CoolNamesAllTaken/radar-speed-sign/affinity/radar_speed_sign.png

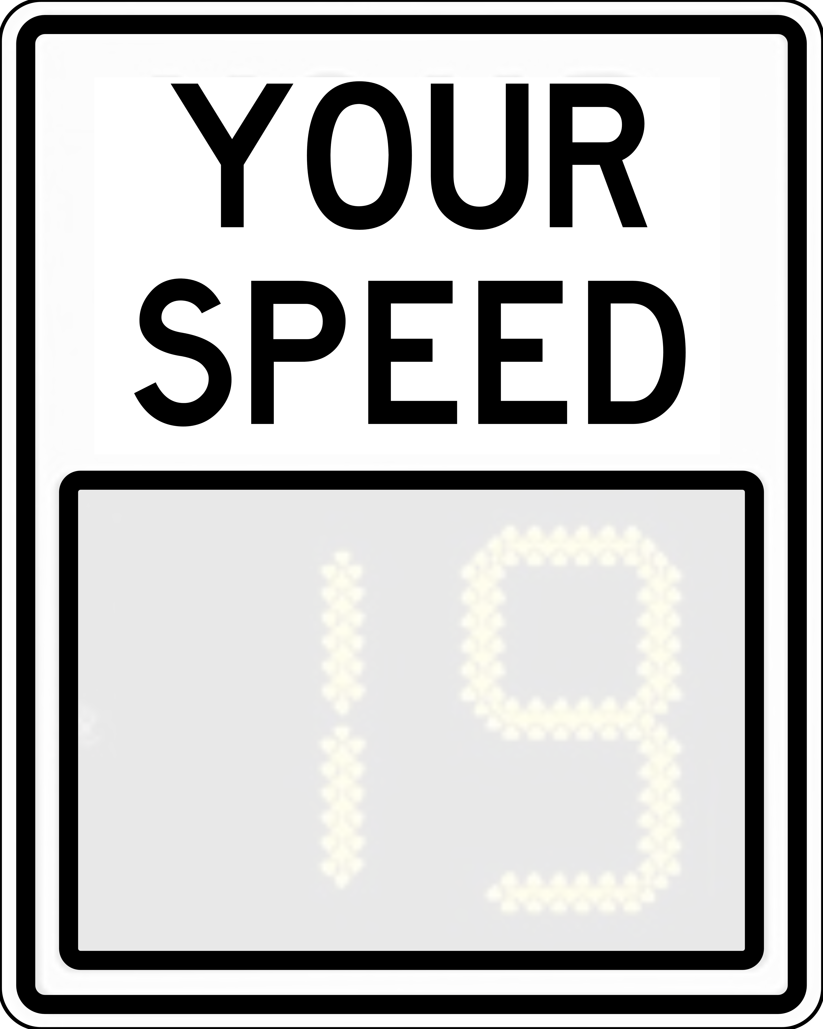
affinity/radar_speed_sign.png
