CoolNamesAllTaken/radar-speed-sign/references/andreas_spiess_radars_comparison.png

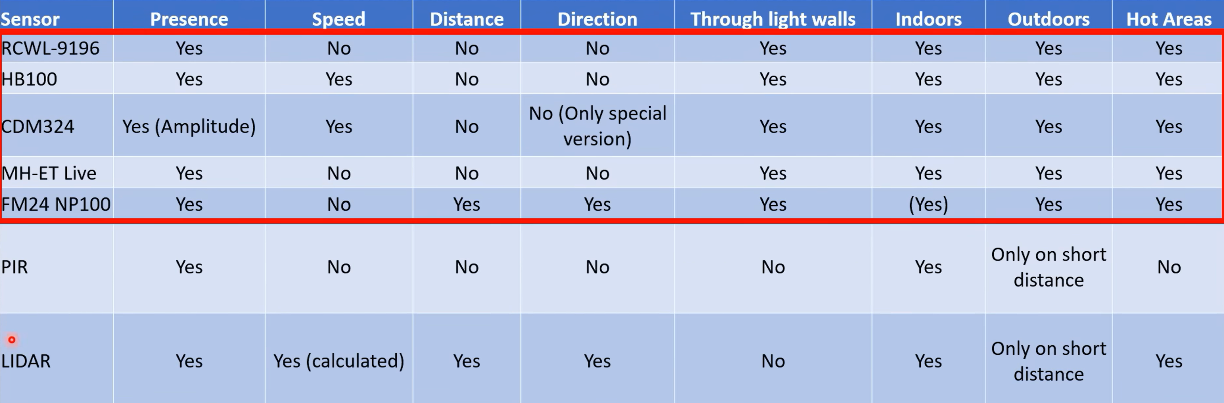
references/andreas_spiess_radars_comparison.png
