CoolNamesAllTaken/radar-speed-sign/references/CDM324 Doppler Speed Sensor, with FFTs! - Limpkin's blog_files/cdm324_digital.PNG

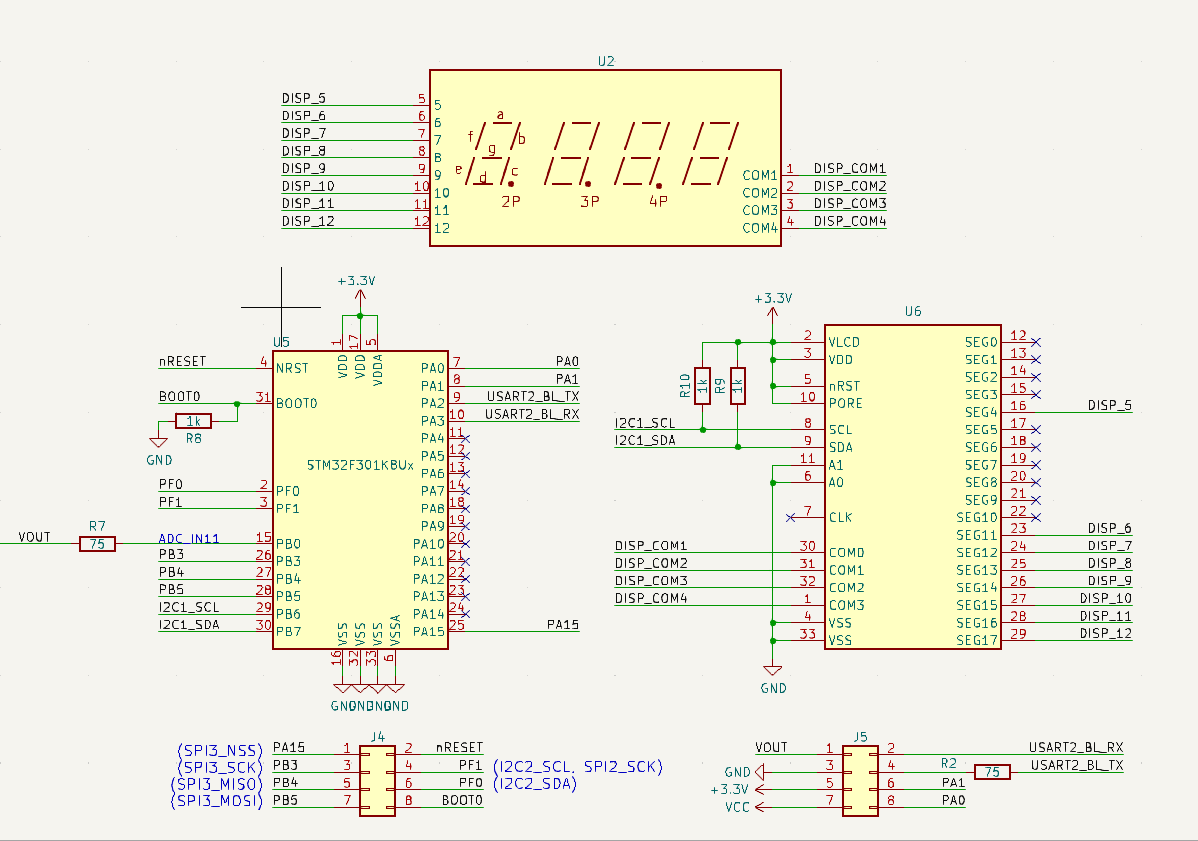
references/CDM324 Doppler Speed Sensor, with FFTs! - Limpkin's blog_files/cdm324_digital.PNG
