CoolNamesAllTaken/radar-speed-sign/references/CDM324 Doppler Speed Sensor, with FFTs! - Limpkin's blog_files/cdm_and_exp.JPG

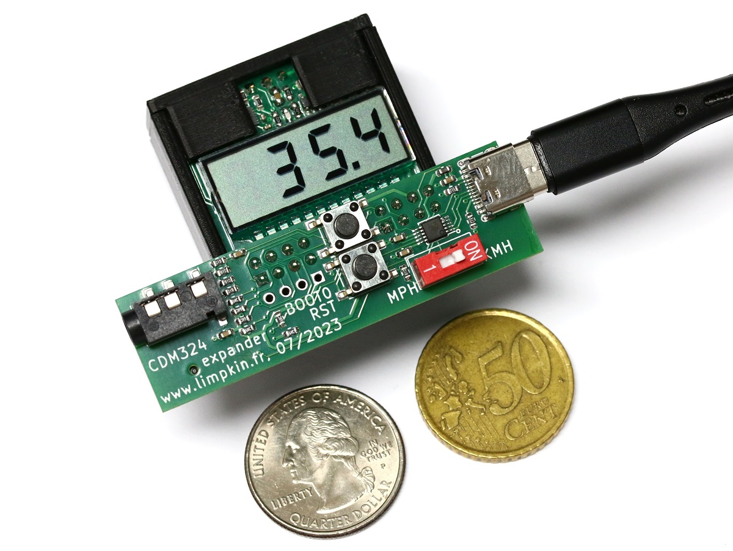
references/CDM324 Doppler Speed Sensor, with FFTs! - Limpkin's blog_files/cdm_and_exp.JPG
