CoolNamesAllTaken/radar-speed-sign/references/CDM324 Doppler Speed Sensor, with FFTs! - Limpkin's blog_files/cdm_pcb.JPG

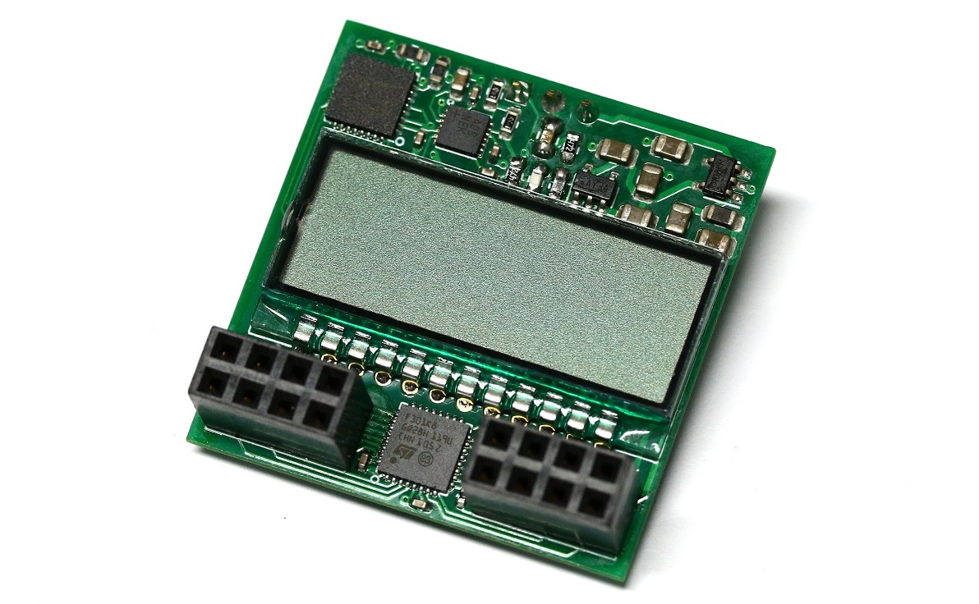
references/CDM324 Doppler Speed Sensor, with FFTs! - Limpkin's blog_files/cdm_pcb.JPG
