CoolNamesAllTaken/radar-speed-sign/references/CDM324 Doppler Speed Sensor, with FFTs! - Limpkin's blog_files/cdm_s21.PNG

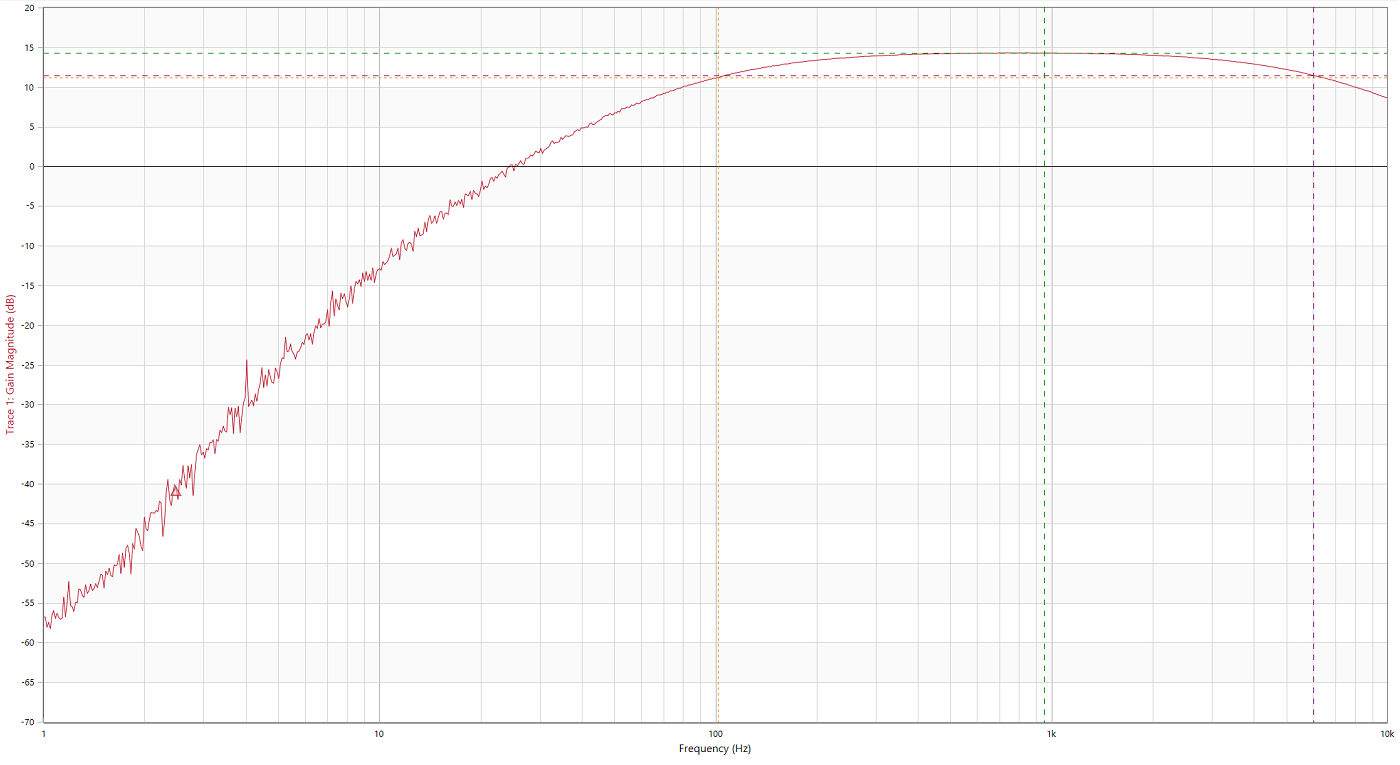
references/CDM324 Doppler Speed Sensor, with FFTs! - Limpkin's blog_files/cdm_s21.PNG
