CoolNamesAllTaken/radar-speed-sign/references/CDM324 Doppler Speed Sensor, with FFTs! - Limpkin's blog_files/disappearing_noise.jpg

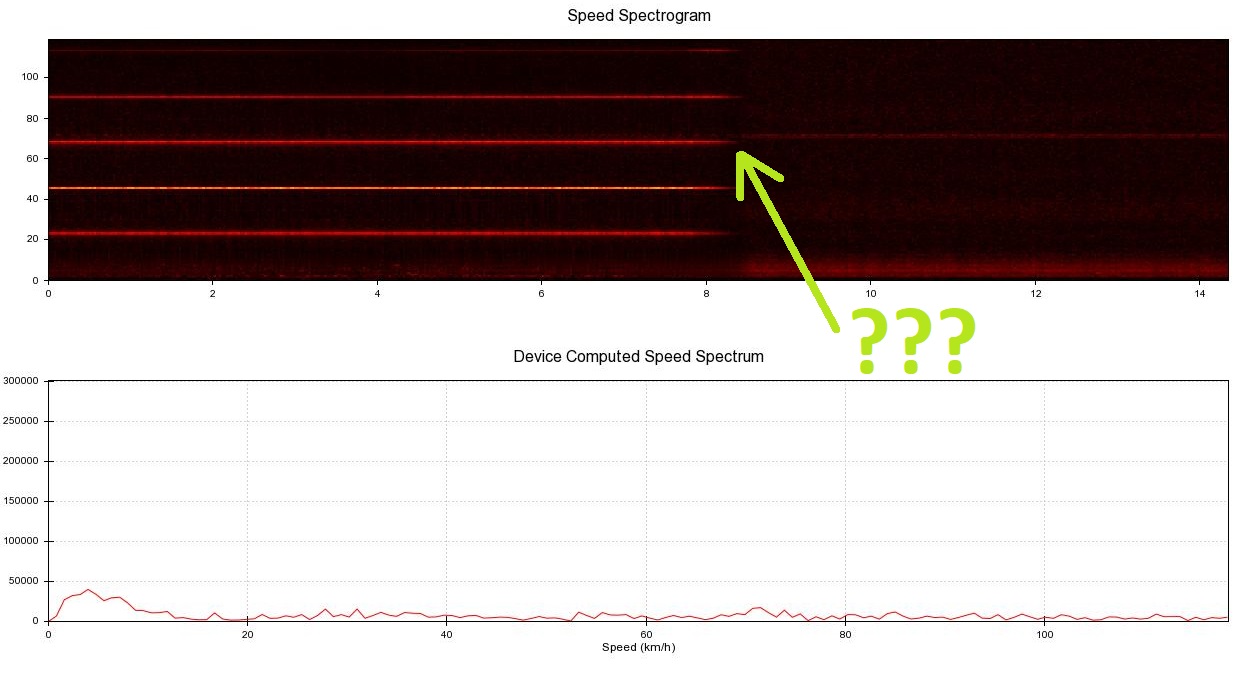
references/CDM324 Doppler Speed Sensor, with FFTs! - Limpkin's blog_files/disappearing_noise.jpg
