CoolNamesAllTaken/radar-speed-sign/references/CDM324 Doppler Speed Sensor, with FFTs! - Limpkin's blog_files/inv_opamp_noise_calc.png

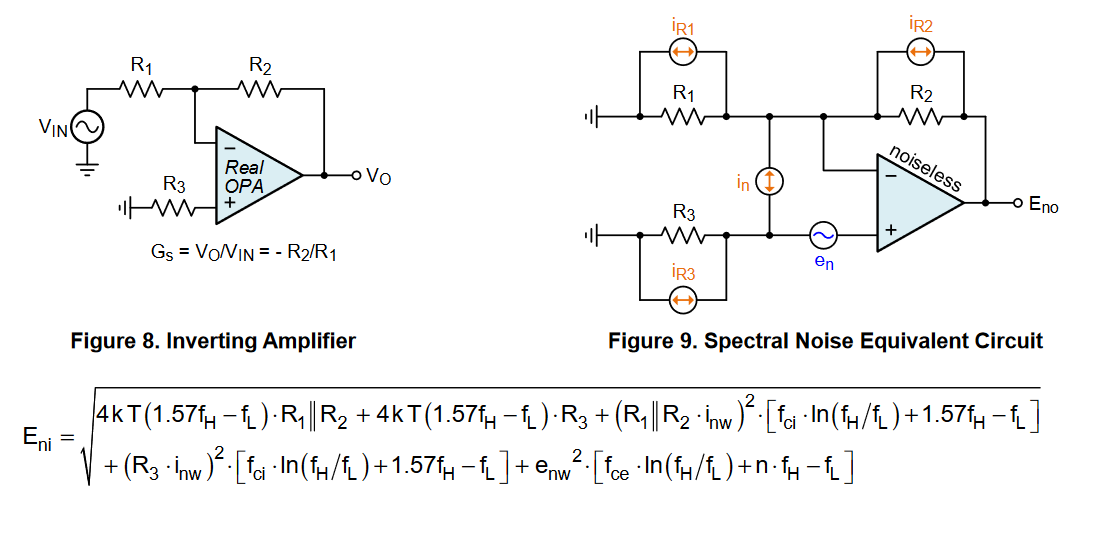
references/CDM324 Doppler Speed Sensor, with FFTs! - Limpkin's blog_files/inv_opamp_noise_calc.png
