CoolNamesAllTaken/radar-speed-sign/references/CDM324 Doppler Speed Sensor, with FFTs! - Limpkin's blog_files/max9814_gain.PNG

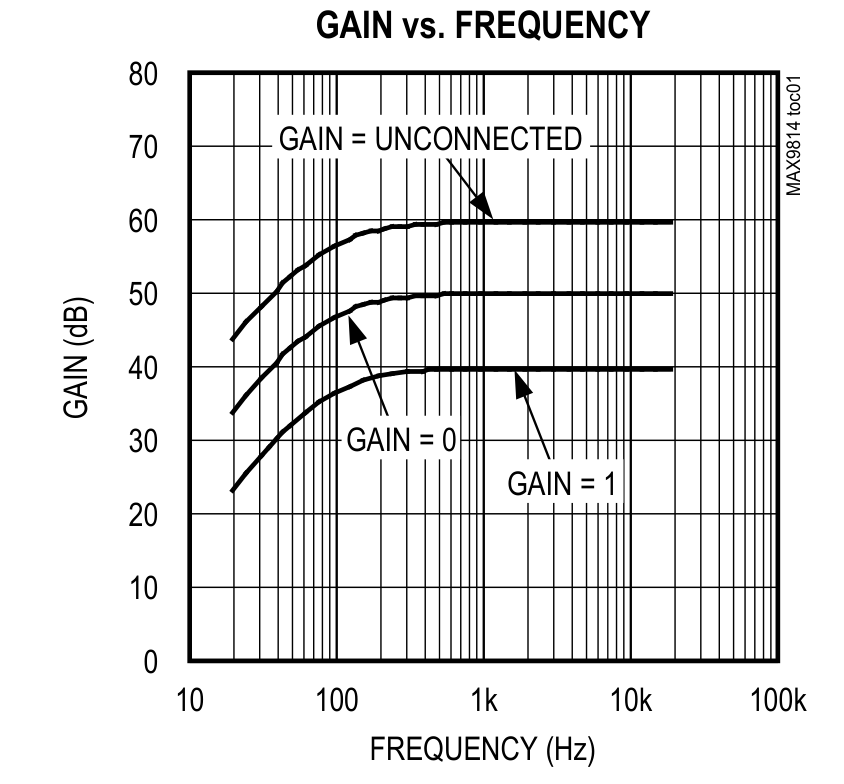
references/CDM324 Doppler Speed Sensor, with FFTs! - Limpkin's blog_files/max9814_gain.PNG
