CoolNamesAllTaken/radar-speed-sign/references/CDM324 Doppler Speed Sensor, with FFTs! - Limpkin's blog_files/Omicron_BODE-100.jpg

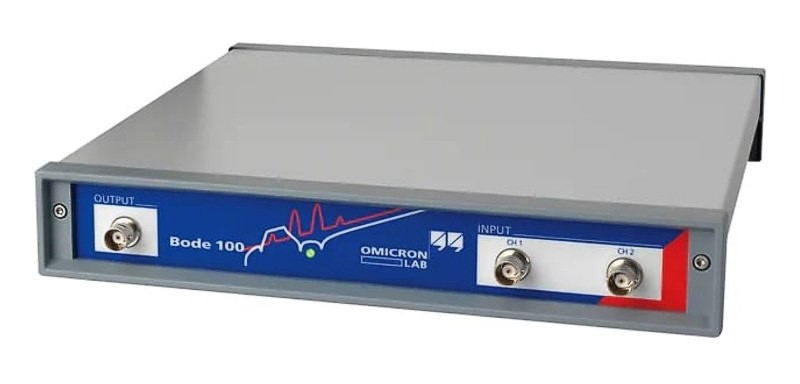
references/CDM324 Doppler Speed Sensor, with FFTs! - Limpkin's blog_files/Omicron_BODE-100.jpg
