CoolNamesAllTaken/radar-speed-sign/references/CDM324 Doppler Speed Sensor, with FFTs! - Limpkin's blog_files/tn_display.PNG

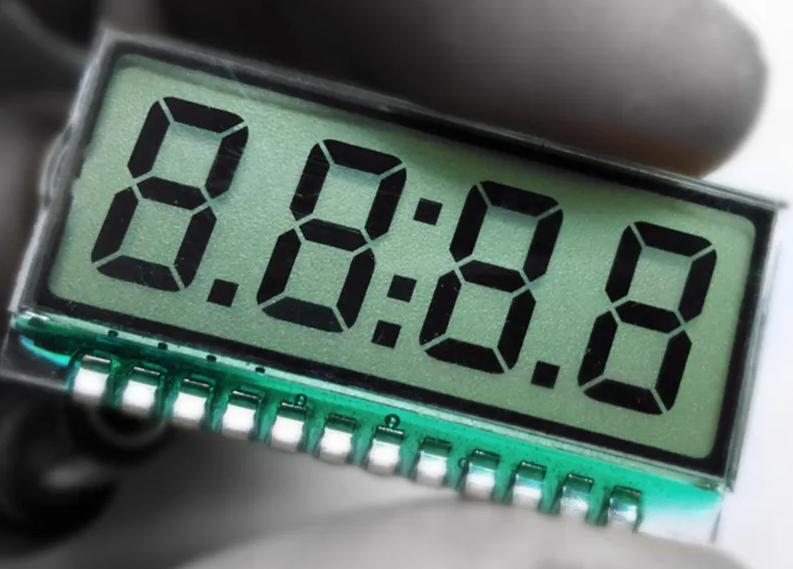
references/CDM324 Doppler Speed Sensor, with FFTs! - Limpkin's blog_files/tn_display.PNG
