CoolNamesAllTaken/radar-speed-sign/references/CDM324 Doppler Speed Sensor, with FFTs! - Limpkin's blog_files/transf_func_cdm324_updated_filter.png

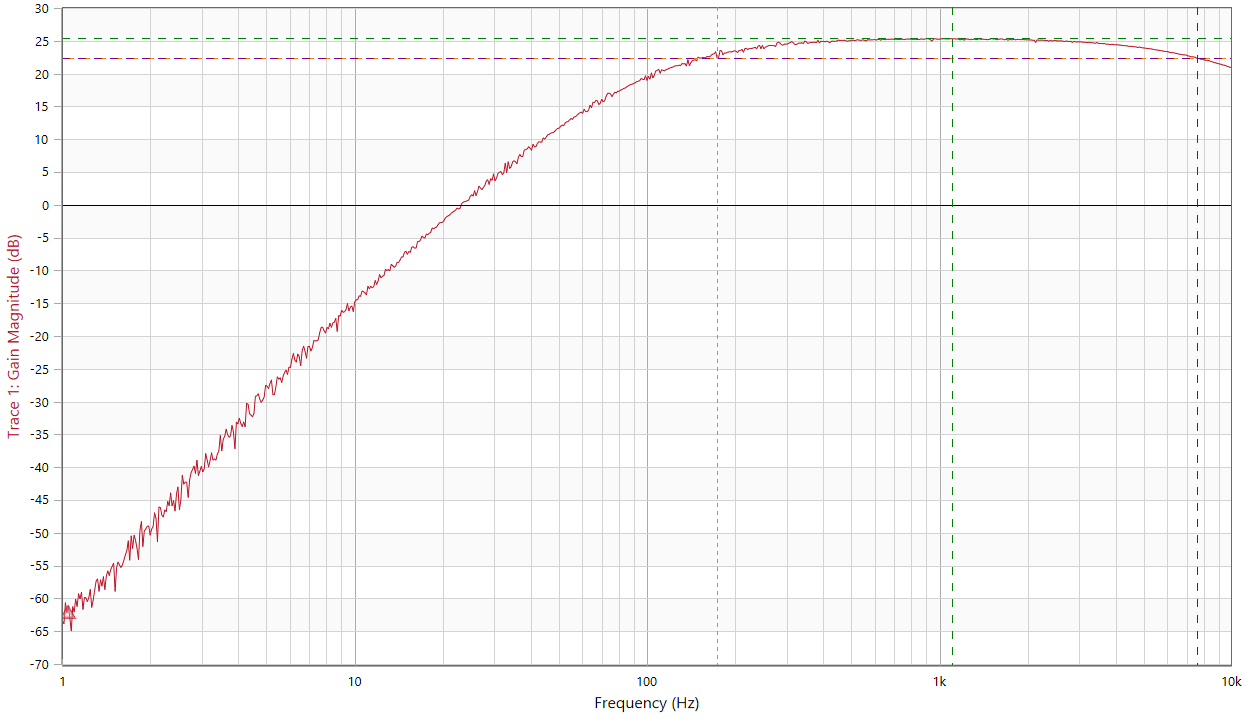
references/CDM324 Doppler Speed Sensor, with FFTs! - Limpkin's blog_files/transf_func_cdm324_updated_filter.png
