CoolNamesAllTaken/radar-speed-sign/references/CDM324 Doppler Speed Sensor, with FFTs! - Limpkin's blog_files/updated_first_stage.PNG

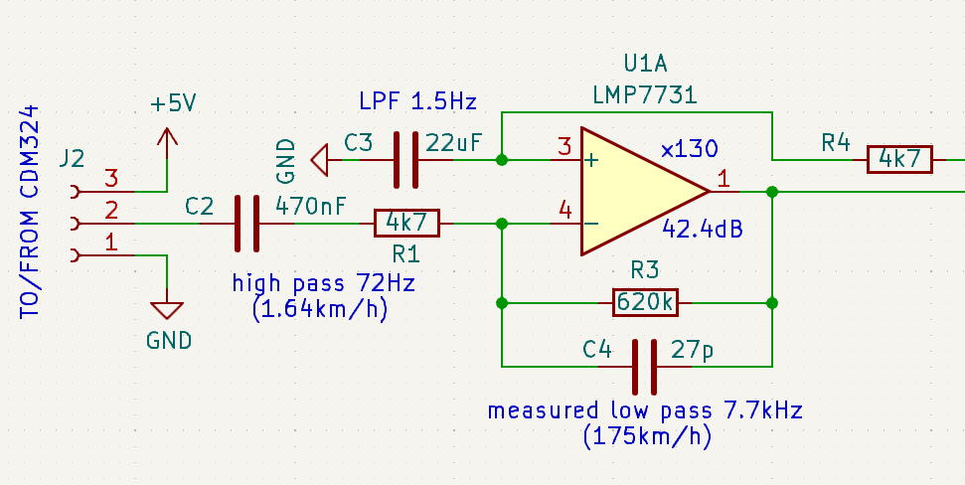
references/CDM324 Doppler Speed Sensor, with FFTs! - Limpkin's blog_files/updated_first_stage.PNG
