CoolNamesAllTaken/radar-speed-sign/references/CDM324 Doppler Speed Sensor, with FFTs! - Limpkin's blog_files/usb_isolator.png

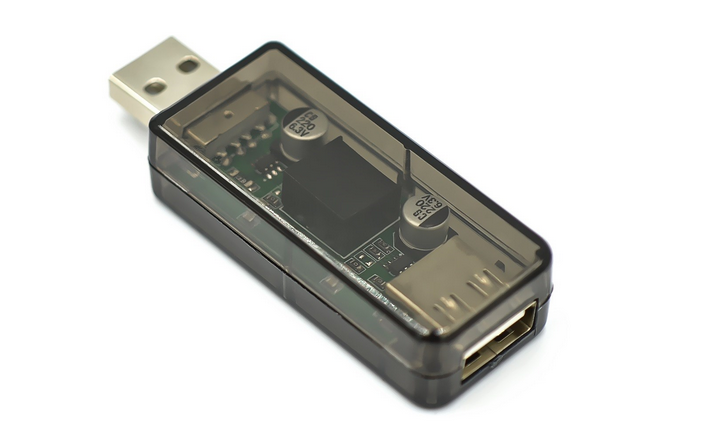
references/CDM324 Doppler Speed Sensor, with FFTs! - Limpkin's blog_files/usb_isolator.png
