CoolNamesAllTaken/radar-speed-sign/references/Radar Module EIRP Radiation Patterns for RCWL-0516, HB100, CDM324_files/CDM324-Radar-Module-Antenna-Pattern-Anechoic-Chamber-Photo-1-683x1024.jpg

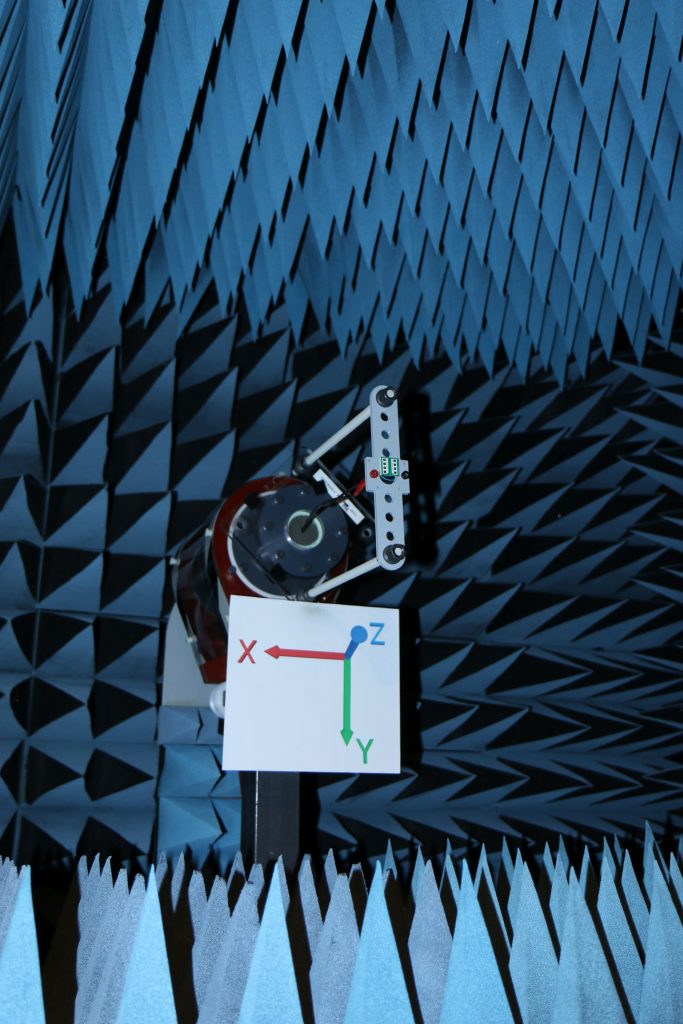
references/Radar Module EIRP Radiation Patterns for RCWL-0516, HB100, CDM324_files/CDM324-Radar-Module-Antenna-Pattern-Anechoic-Chamber-Photo-1-683x1024.jpg
