CoolNamesAllTaken/radar-speed-sign/references/Radar Module EIRP Radiation Patterns for RCWL-0516, HB100, CDM324_files/HB100-Module-PCB.jpg

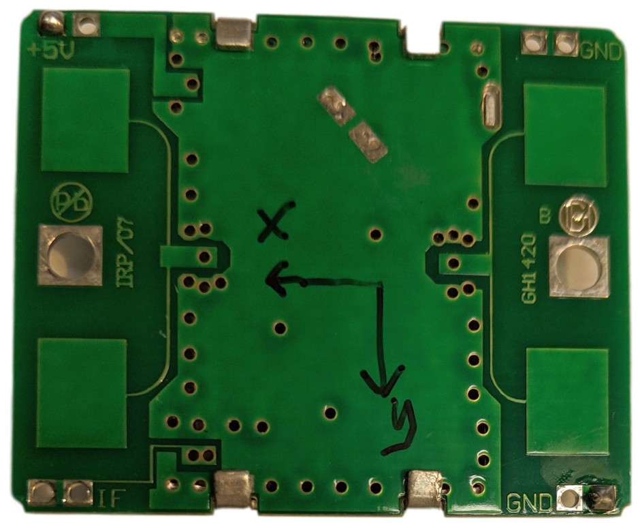
references/Radar Module EIRP Radiation Patterns for RCWL-0516, HB100, CDM324_files/HB100-Module-PCB.jpg
