CoolNamesAllTaken/radar-speed-sign/references/Radar Module EIRP Radiation Patterns for RCWL-0516, HB100, CDM324_files/HB100-Radar-Module-Antenna-Pattern-Anechoic-Chamber-Photo-1-1024x647.jpg

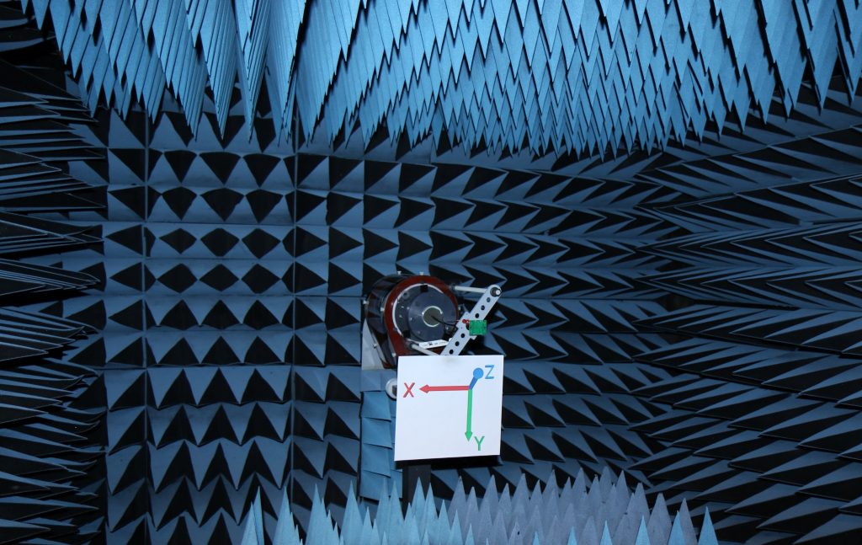
references/Radar Module EIRP Radiation Patterns for RCWL-0516, HB100, CDM324_files/HB100-Radar-Module-Antenna-Pattern-Anechoic-Chamber-Photo-1-1024x647.jpg
