CoolNamesAllTaken/radar-speed-sign/references/Radar Module EIRP Radiation Patterns for RCWL-0516, HB100, CDM324_files/HB100-Radar-Module-Antenna-Pattern-Anechoic-Chamber-Photo-4-1024x683.jpg

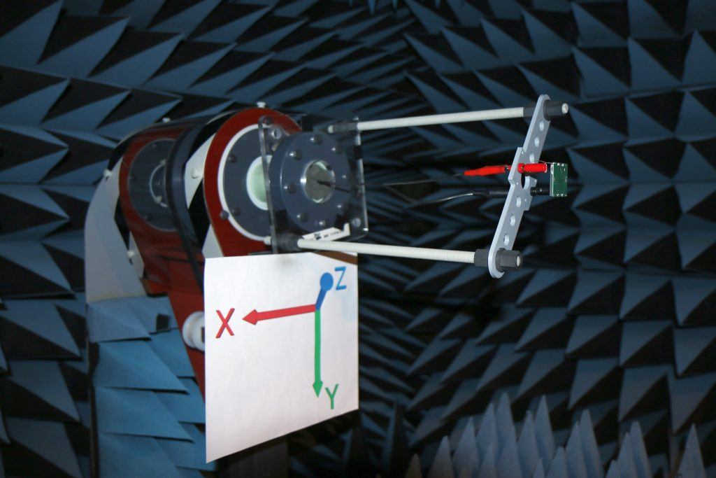
references/Radar Module EIRP Radiation Patterns for RCWL-0516, HB100, CDM324_files/HB100-Radar-Module-Antenna-Pattern-Anechoic-Chamber-Photo-4-1024x683.jpg
