CoolNamesAllTaken/radar-speed-sign/references/Radar Module EIRP Radiation Patterns for RCWL-0516, HB100, CDM324_files/RCWL-0516-Radar-Module-Antenna-Pattern-Anechoic-Chamber-Photo-1-813x1024.jpg

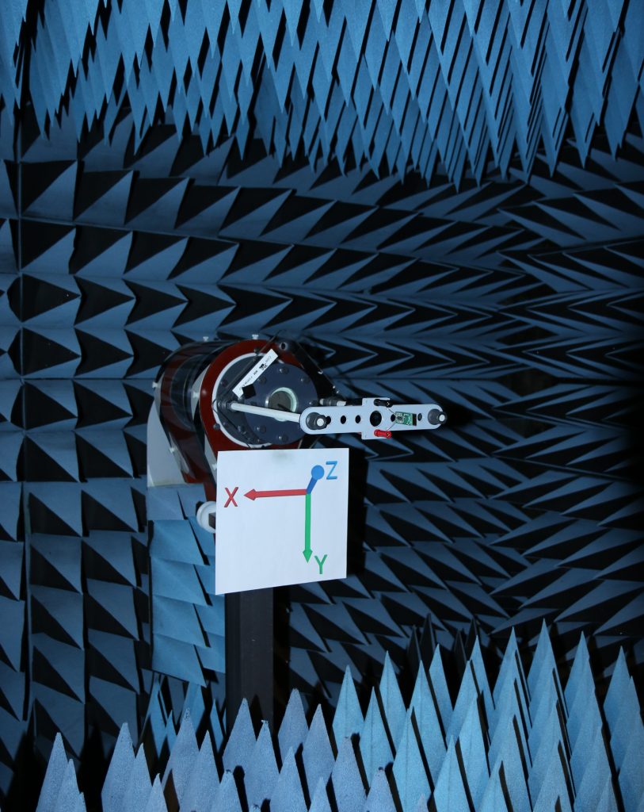
references/Radar Module EIRP Radiation Patterns for RCWL-0516, HB100, CDM324_files/RCWL-0516-Radar-Module-Antenna-Pattern-Anechoic-Chamber-Photo-1-813x1024.jpg
