CoolNamesAllTaken/radar-speed-sign/references/CDM324 Doppler Speed Sensor, with FFTs! - Limpkin's blog_files/cdm324_cur_transient_issue.png

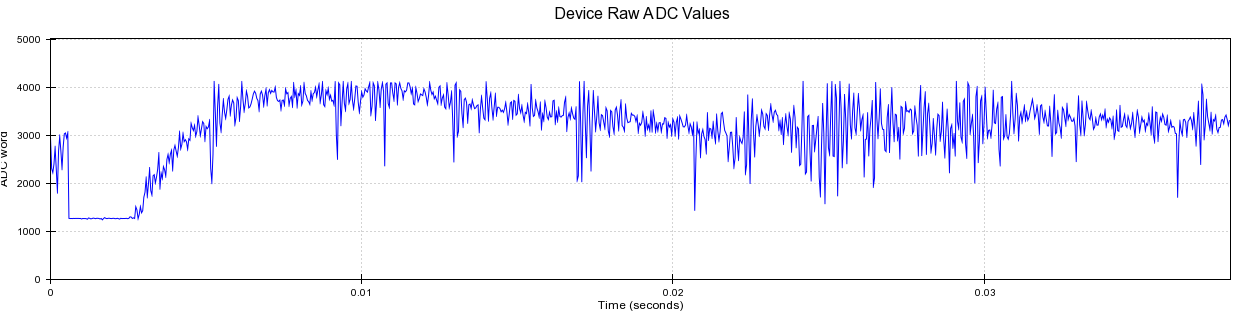
references/CDM324 Doppler Speed Sensor, with FFTs! - Limpkin's blog_files/cdm324_cur_transient_issue.png
