CoolNamesAllTaken/radar-speed-sign/ltspice/lm358_amplifier_bode.asc

C1: cap; 4.7µ
C3: cap; 4.7µ
C4: cap; 4.7µ
R1: res; 10k
R2: res; 10k
U1: UniversalOpAmp2
V1: voltage; ""; AC 1
Named nets: 3v3, 0, in, out
.ac dec 1000 1 100k
