CoolNamesAllTaken/radar-speed-sign/code/pico_cpp_radar_speed_sign/src/fft_utils.cpp

#include "fft_utils.hh"
#include "stdio.h" // for printing

const uint16_t kNumHanningSteps = 1000;
uint16_t kHanningTableUint16[kNumHanningSteps] = {
        0, 0, 1, 3, 5, 8, 12, 16, 21, 26, 32,
        39, 47, 55, 63, 73, 83, 93, 105, 117, 129,
        142, 156, 171, 186, 202, 218, 235, 253, 271, 290,
        310, 330, 351, 372, 395, 417, 441, 465, 489, 515,
        541, 567, 594, 622, 651, 680, 709, 739, 770, 802,
        834, 867, 900, 934, 969, 1004, 1040, 1076, 1113, 1151,
        1189, 1228, 1267, 1307, 1348, 1389, 1430, 1473, 1516, 1559,
        1603, 1648, 1693, 1739, 1786, 1833, 1880, 1929, 1977, 2027,
        2076, 2127, 2178, 2229, 2282, 2334, 2388, 2441, 2496, 2551,
        2606, 2662, 2718, 2776, 2833, 2891, 2950, 3009, 3069, 3129,
        3190, 3251, 3313, 3375, 3438, 3501, 3565, 3630, 3695, 3760,
        3826, 3892, 3959, 4026, 4094, 4163, 4231, 4301, 4370, 4441,
        4511, 4582, 4654, 4726, 4799, 4872, 4945, 5019, 5094, 5168,
        5244, 5319, 5395, 5472, 5549, 5626, 5704, 5783, 5861, 5940,
        6020, 6100, 6180, 6261, 6342, 6424, 6506, 6588, 6671, 6754,
        6837, 6921, 7005, 7090, 7175, 7260, 7346, 7432, 7518, 7605,
        7692, 7780, 7867, 7955, 8044, 8133, 8222, 8311, 8401, 8491,
        8581, 8672, 8763, 8854, 8946, 9038, 9130, 9222, 9315, 9408,
        9501, 9595, 9689, 9783, 9877, 9972, 10067, 10162, 10257, 10353,
        10448, 10545, 10641, 10737, 10834, 10931, 11028, 11126, 11223, 11321,
        11419, 11517, 11616, 11714, 11813, 11912, 12011, 12110, 12210, 12309,
        12409, 12509, 12609, 12710, 12810, 12910, 13011, 13112, 13213, 13314,
        13415, 13516, 13618, 13719, 13821, 13923, 14025, 14126, 14228, 14331,
        14433, 14535, 14637, 14740, 14842, 14945, 15047, 15150, 15253, 15355,
        15458, 15561, 15664, 15766, 15869, 15972, 16075, 16178, 16281, 16384,
        16487, 16590, 16693, 16796, 16899, 17002, 17104, 17207, 17310, 17413,
        17515, 17618, 17721, 17823, 17926, 18028, 18131, 18233, 18335, 18437,
        18540, 18642, 18743, 18845, 18947, 19049, 19150, 19252, 19353, 19454,
        19555, 19656, 19757, 19858, 19958, 20058, 20159, 20259, 20359, 20459,
        20558, 20658, 20757, 20856, 20955, 21054, 21152, 21251, 21349, 21447,
        21545, 21642, 21740, 21837, 21934, 22031, 22127, 22223, 22320, 22415,
        22511, 22606, 22701, 22796, 22891, 22985, 23079, 23173, 23267, 23360,
        23453, 23546, 23638, 23730, 23822, 23914, 24005, 24096, 24187, 24277,
        24367, 24457, 24546, 24635, 24724, 24813, 24901, 24988, 25076, 25163,
        25250, 25336, 25422, 25508, 25593, 25678, 25763, 25847, 25931, 26014,
        26097, 26180, 26262, 26344, 26426, 26507, 26588, 26668, 26748, 26828,
        26907, 26985, 27064, 27142, 27219, 27296, 27373, 27449, 27524, 27600,
        27674, 27749, 27823, 27896, 27969, 28042, 28114, 28186, 28257, 28327,
        28398, 28467, 28537, 28605, 28674, 28742, 28809, 28876, 28942, 29008,
        29073, 29138, 29203, 29267, 29330, 29393, 29455, 29517, 29578, 29639,
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
};

/**
 * @brief Apply a Hanning sine function to a buffer of uint16_t's. Does this by mutliplying by
 * uint16_t's and storing the result as an uint32_t, which then gets right shifted to divide by
 * UINT16_T_MAX and convert back into an uint16.
 * @param[in] buf Pointer to buffer with buf_size elements. Will be modified in-place.
 * @param[in] buf_size Number of elements in buf. Must be equal to kNumHanningSteps.
*/
void ApplyHanningWindowUint16(uint16_t * buf, uint16_t buf_size) {
    if (buf_size != kNumHanningSteps) {
        // TODO: Could do some kind of fancy interpolation thing here in the future.
        printf("ApplyHanningWindow16: Error, expected buf of size %d but got buf of size %d.\r\n", kNumHanningSteps, buf_size);
        return;
    }

    for (uint16_t i = 0; i < buf_size; i++) {
        buf[i] = static_cast<uint16_t>((static_cast<uint32_t>(buf[i]) * static_cast<uint32_t>(kHanningTableUint16[i]))>>16);
    }
}
